faerietree/manipulator/estimation_weight_liftable.jpg

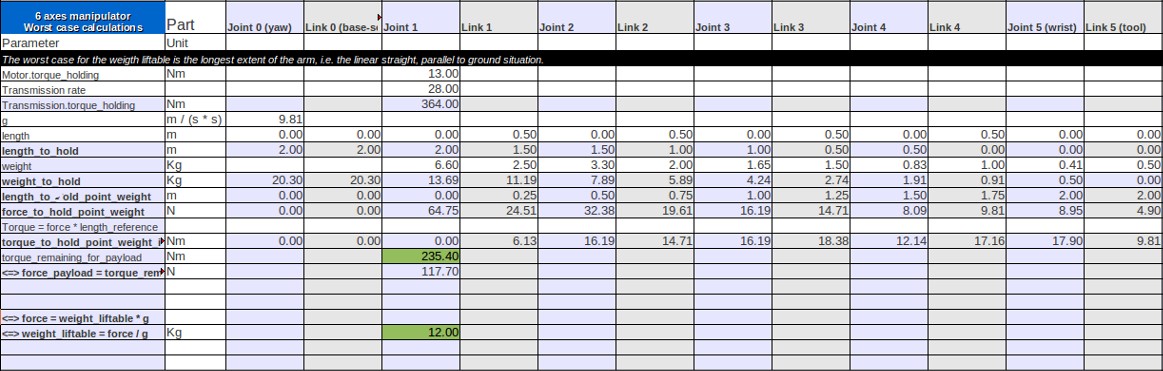
estimation_weight_liftable.jpg
