faerietree/manipulator/transmission_ratio_28_side.jpg

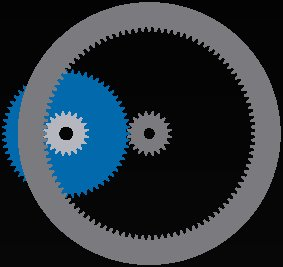
transmission_ratio_28_side.jpg
